pudding1232/Light-Buddy/images/cad-v1-base.png

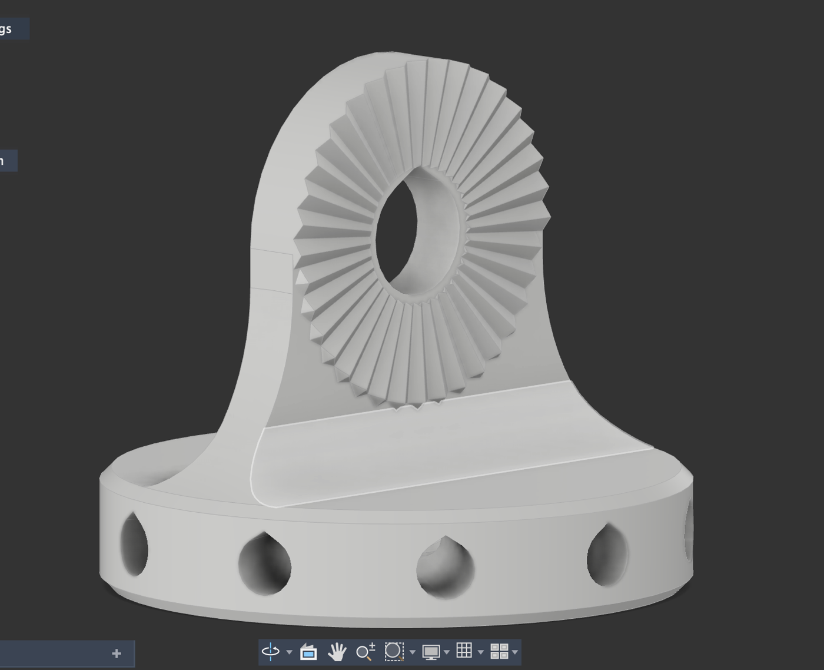
images/cad-v1-base.png
