pudding1232/Light-Buddy/images/cad-v1-vblock-1.png

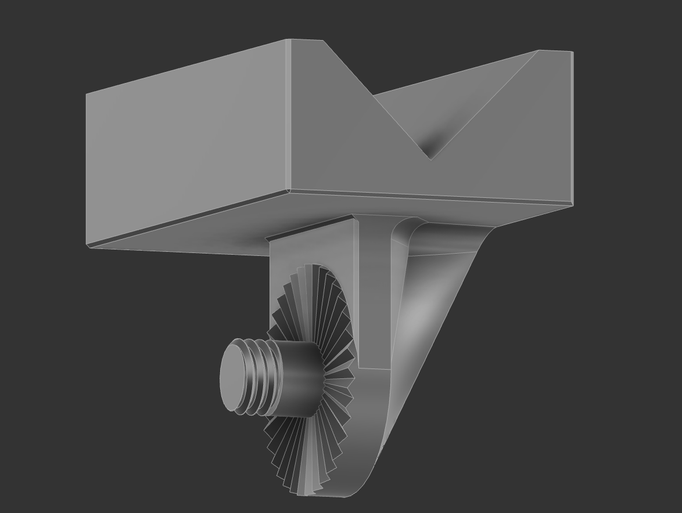
images/cad-v1-vblock-1.png
