pudding1232/Light-Buddy/images/cad-v1-vblock-2.png

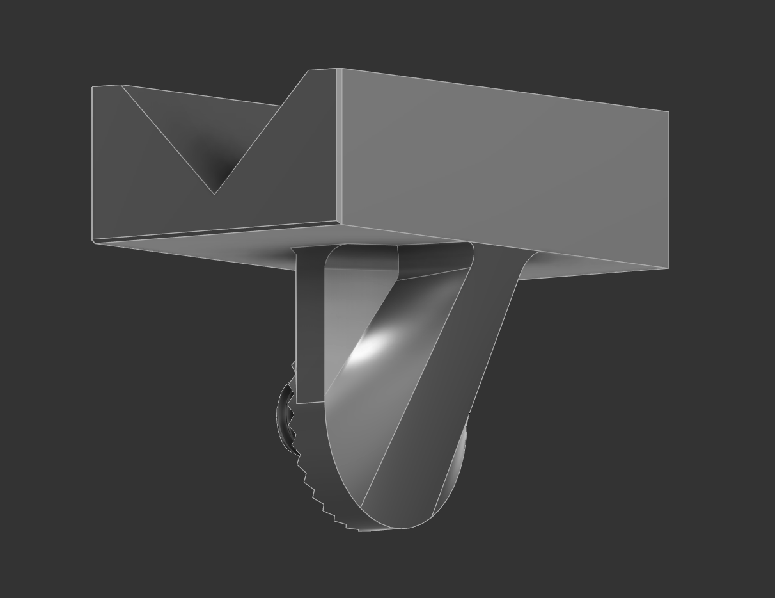
images/cad-v1-vblock-2.png
