pudding1232/Light-Buddy/images/cad-v2-ratchet-base-bottom.png

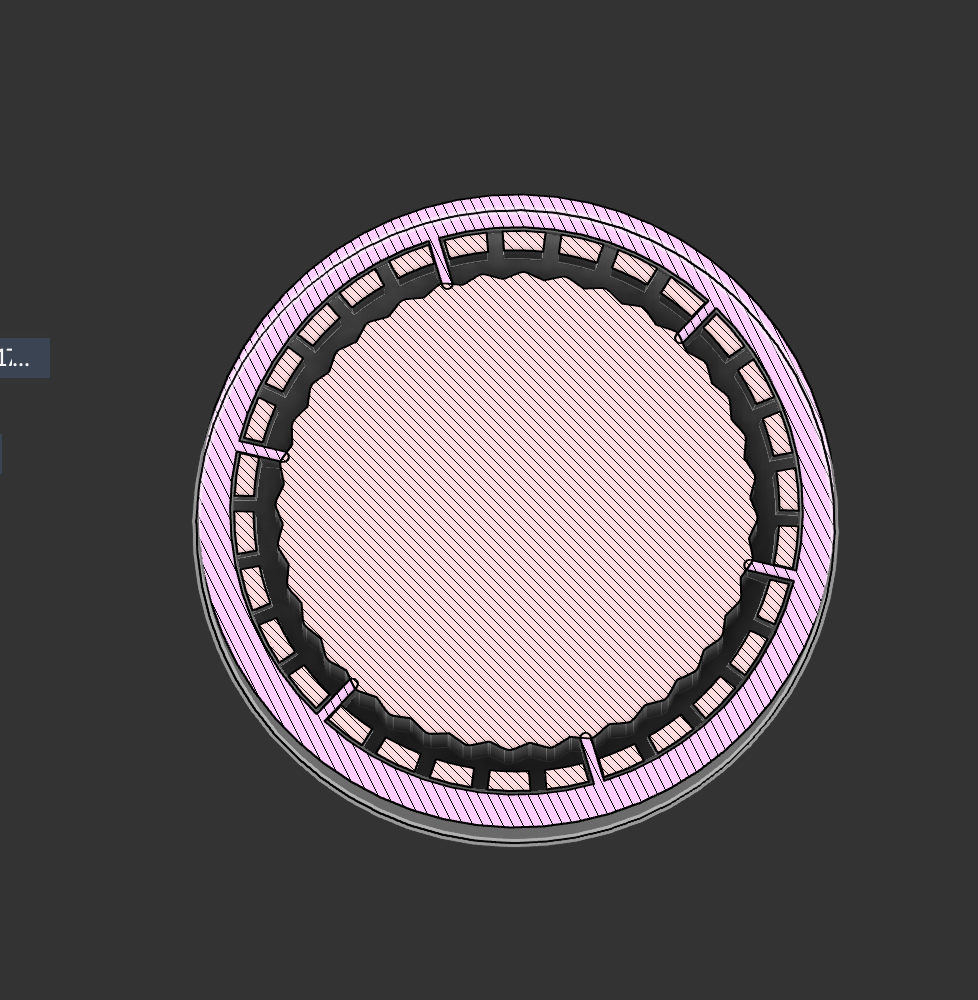
images/cad-v2-ratchet-base-bottom.png
