pudding1232/Light-Buddy/images/cad-v2-strap-loops.png

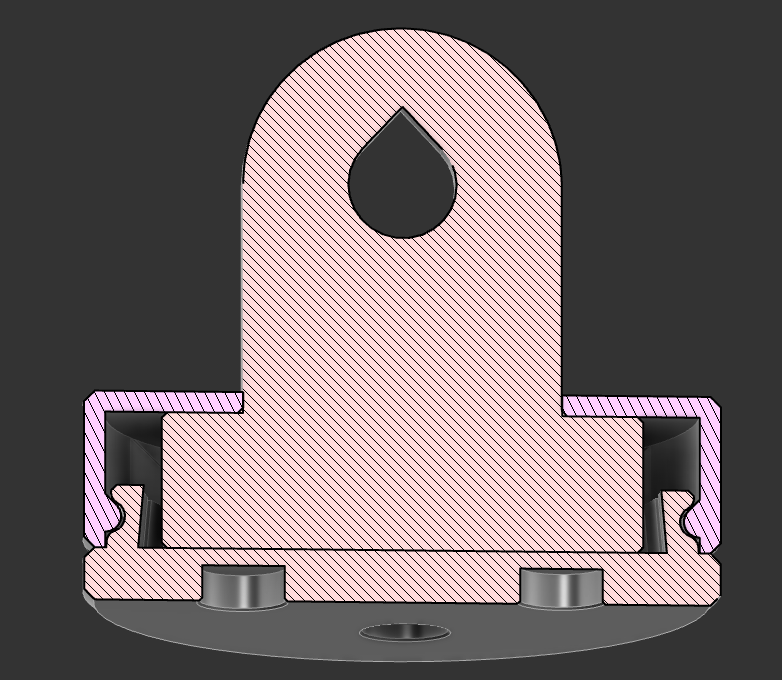
images/cad-v2-strap-loops.png
