pudding1232/Light-Buddy/images/cad-v3-base-lip.png

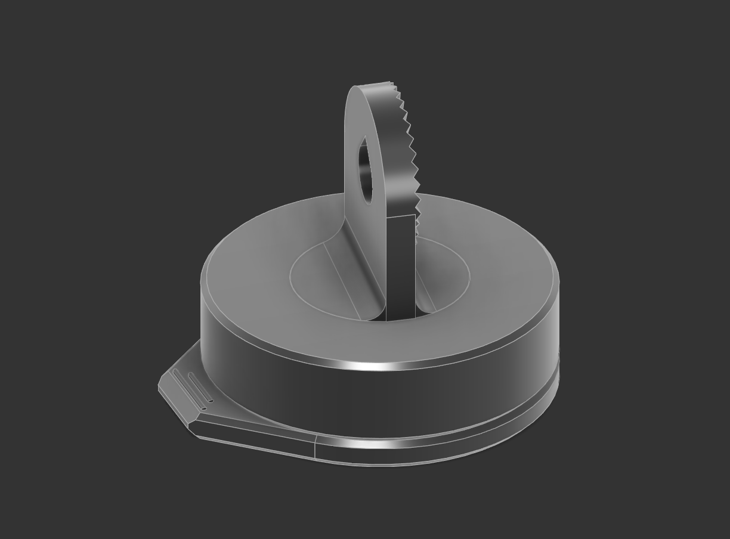
images/cad-v3-base-lip.png
