pudding1232/Light-Buddy/images/v1-base-joint.jpg

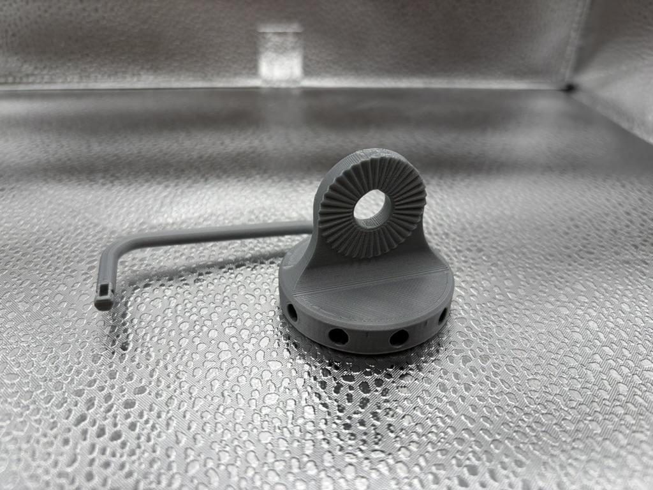
images/v1-base-joint.jpg
