pudding1232/Light-Buddy/images/v2-ratchet-housing.jpg

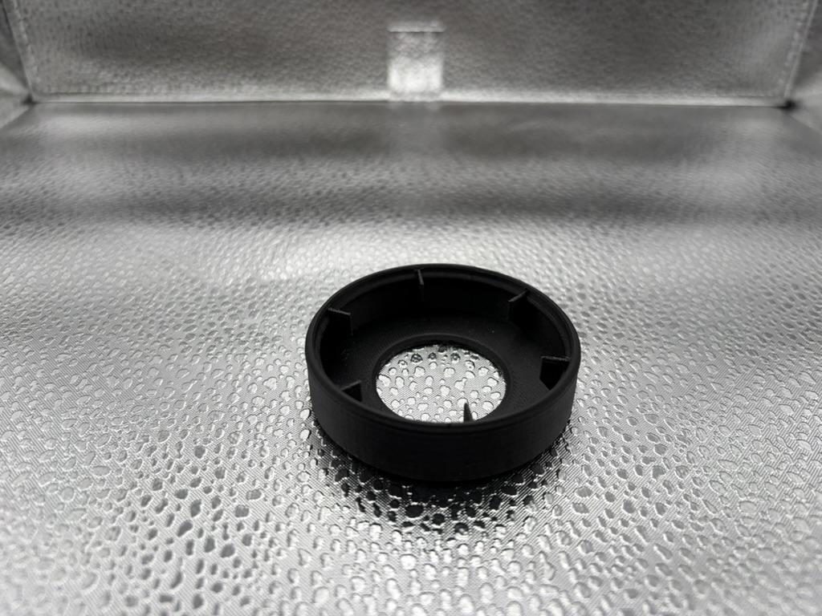
images/v2-ratchet-housing.jpg
