pudding1232/Light-Buddy/images/v3-nut-polyjet-1.jpg

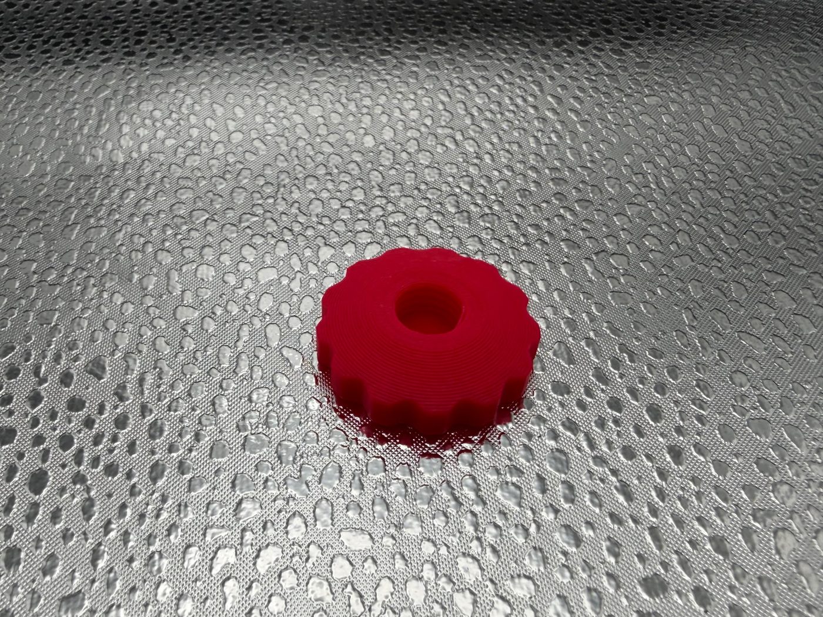
images/v3-nut-polyjet-1.jpg
