pudding1232/Light-Buddy/images/v3-nut-polyjet-3.jpg

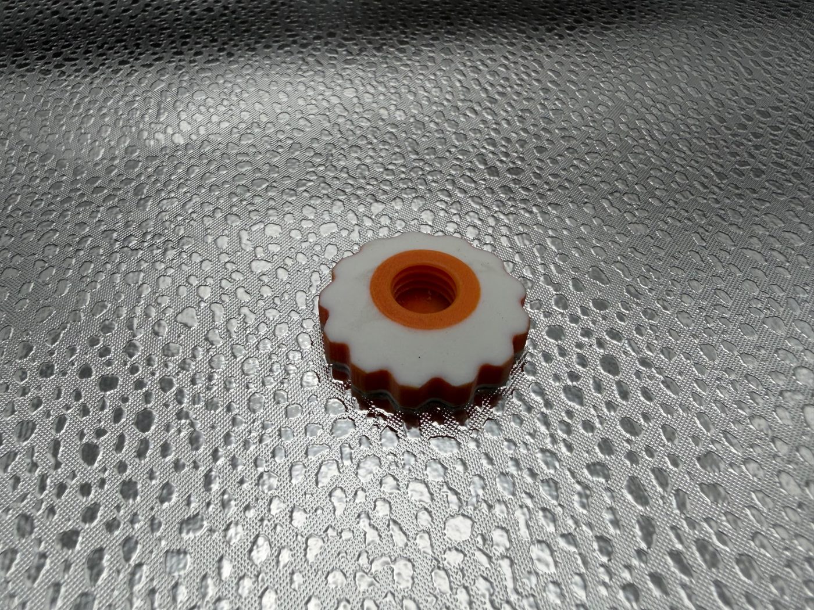
images/v3-nut-polyjet-3.jpg
