pudding1232/Light-Buddy/images/v3-vblock-straps-2.jpg

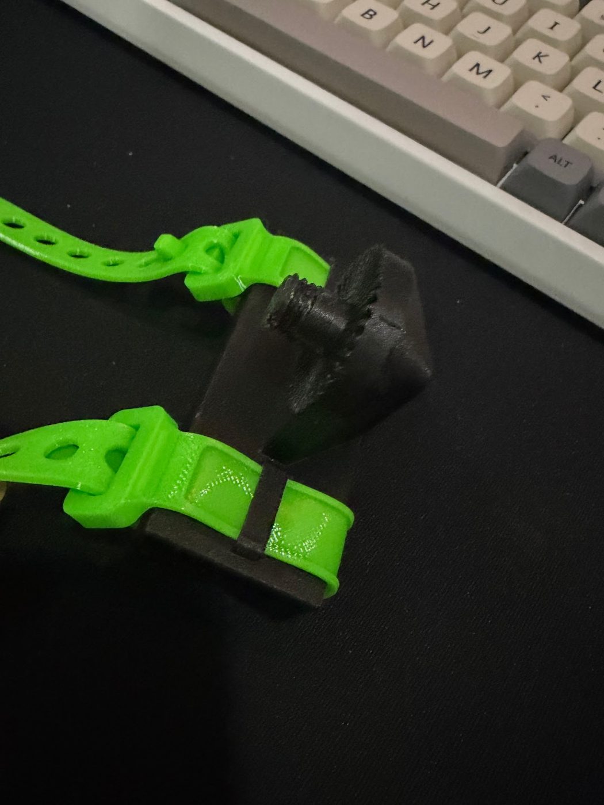
images/v3-vblock-straps-2.jpg
