pudding1232/Light-Buddy/images/vblock-v1-v3-side.jpg

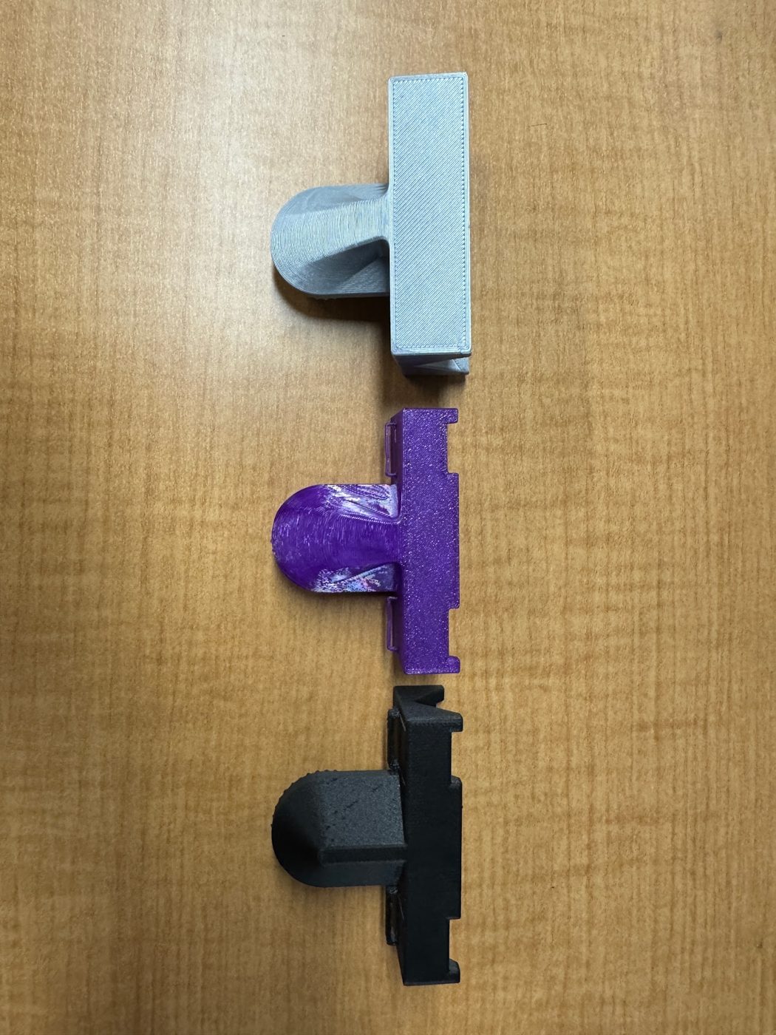
images/vblock-v1-v3-side.jpg
